Khansday/Data-collector/Codes to test each module of the system/Lidar_checksum/Lidar_checksum.ino

/*
~~~~RETRIEVE PACKETS FROM LIDAR WITH TIMOUT AND FILLS A CIRCULAR BUFFER
~~~~NEW DATA IN THE BUFFER IS READ AND PROCESSED
~~~~ ALL ANGLES ARE ROUNDED TO LOWEST 10, PACKETS REGARDING TO THAT ANGLE, THE MIN DISTNACE IS UPDATED.
*/


#include <Arduino.h>
#include "mbed.h"  // Include Mbed OS headers to apply mbed_app.json configurations

#define BUFFER_SIZE 10000 // Define the size of the buffer
byte raw_array[BUFFER_SIZE] = {0};  // Initialize the buffer

// Circular buffer indices and counters
volatile size_t read_index = 0;
volatile size_t write_index = 0;
volatile size_t buffer_count = 0;

bool new_lidar_data_flag = false;

// Modifiable time limits (in milliseconds)
unsigned long buffer_fill_time_limit = 10; // Time limit for filling the buffer
unsigned long parsing_time_limit = 2;     // Time limit for parsing the buffer

const int NUM_ANGLES = 19; // Represents angles from 0 to 180 in steps of 10 degrees
int min_distances[NUM_ANGLES];

void setup() {
  Serial.begin(500000);    // Start the serial port for logging
  Serial1.begin(230400);   // Start Serial1 to communicate with the LiDAR module

  delay(1000);
  Serial.println("Program Started");
  delay(1000);

  init_distance_array();
}

void loop() {
  // Fill the buffer with data from LiDAR for a specified time or until full
  full_raw_buffer();

  // Parse the buffer at specified intervals with a time limit
  if (new_lidar_data_flag) {
    parse_raw_buffer_min_angle();
    new_lidar_data_flag = false; // Reset the flag after parsing
  } else {
    Serial.println("No new data");
  }
}

void full_raw_buffer() {
  unsigned long start_time = millis();

  while (millis() - start_time < buffer_fill_time_limit && buffer_count < BUFFER_SIZE) {
    if (Serial1.available()) {
      int data = Serial1.read();
      if (data != -1) {
        // Check if buffer is not full
        if (buffer_count < BUFFER_SIZE) {
          raw_array[write_index++] = (byte)data;
          write_index %= BUFFER_SIZE;
          buffer_count++;
          new_lidar_data_flag = true;
        } else {
          // Buffer is full
          //Serial.println("Buffer is full, cannot write more data");
          break;
        }
      }
    }
  }

  if (millis() - start_time >= buffer_fill_time_limit) {
    //Serial.println("Buffer fill time limit reached");
  }
}

// Function to retrieve the min value from a packet, validate CRC, and update the main distance array
void parse_raw_buffer_min_angle() {
  unsigned long start_time = millis();

  const int PACKET_SIZE = 46;
  const int NUM_POINTS = 12;

  while (millis() - start_time < parsing_time_limit && buffer_count >= PACKET_SIZE) {
    // Check for packet start
    if (raw_array[read_index] == 0x54 && raw_array[(read_index + 1) % BUFFER_SIZE] == 0x2C) {
      // Ensure we have enough data for a full packet
      if (buffer_count >= PACKET_SIZE) {
        // Read packet into a temporary array
        byte packet[PACKET_SIZE];
        for (int i = 0; i < PACKET_SIZE; i++) {
          packet[i] = raw_array[(read_index + i) % BUFFER_SIZE];
        }

        // Calculate CRC8 checksum for the packet (excluding the last byte, which is the CRC)
        byte computed_crc = calculate_crc8(packet, PACKET_SIZE - 1);

        // Compare the computed CRC with the one in the packet
        if (computed_crc == packet[PACKET_SIZE - 1]) {
          // Process the packet if CRC is valid
          float start_angle = (packet[4] + (packet[5] << 8)) * 0.01;
          float end_angle = (packet[42] + (packet[43] << 8)) * 0.01;

          // Approximate start_angle to the lowest ten
          int start_angle_approx = ((int)(start_angle / 10)) * 10;

          // Check if start_angle_approx is between 0 and 180
          if (start_angle_approx >= 0 && start_angle_approx <= 180) {
            int index = start_angle_approx / 10;

            // Read data points and find the minimum distance in this packet
            int min_distance_in_packet = 8000;

            for (int j = 0; j < NUM_POINTS; j++) {
              int idx = 6 + j * 3;
              int distance = packet[idx] + (packet[idx + 1] << 8);
              // Ignore zero distances
              if (distance != 0 && distance < min_distance_in_packet) {
                min_distance_in_packet = distance;
              }
            }

            // Update the min_distances array
            min_distances[index] = min_distance_in_packet;

            Serial.print(start_angle_approx);
            Serial.print("\t\t");
            Serial.print(min_distances[index]);
            Serial.print("\t\t");
            Serial.println("1");
          }
        } else {
          // Handle CRC failure (optional logging)
          Serial.println("CRC mismatch: Packet discarded.");
        }

        // Move read_index forward by PACKET_SIZE
        read_index = (read_index + PACKET_SIZE) % BUFFER_SIZE;
        buffer_count -= PACKET_SIZE;
      } else {
        // Not enough data to read a full packet
        break;
      }
    } else {
      // Move read_index forward by 1
      read_index = (read_index + 1) % BUFFER_SIZE;
      buffer_count--;
    }
  }

  if (millis() - start_time >= parsing_time_limit) {
    //Serial.println("Parsing time limit reached");
  }
}

static const uint8_t CrcTable[256] =
{
    0x00, 0x4d, 0x9a, 0xd7, 0x79, 0x34, 0xe3, 
    0xae, 0xf2, 0xbf, 0x68, 0x25, 0x8b, 0xc6, 0x11, 0x5c, 0xa9, 0xe4, 0x33,
    0x7e, 0xd0, 0x9d, 0x4a, 0x07, 0x5b, 0x16, 0xc1, 0x8c, 0x22, 0x6f, 0xb8,
    0xf5, 0x1f, 0x52, 0x85, 0xc8, 0x66, 0x2b, 0xfc, 0xb1, 0xed, 0xa0, 0x77, 
    0x3a, 0x94, 0xd9, 0x0e, 0x43, 0xb6, 0xfb, 0x2c, 0x61, 0xcf, 0x82, 0x55,
    0x18, 0x44, 0x09, 0xde, 0x93, 0x3d, 0x70, 0xa7, 0xea, 0x3e, 0x73, 0xa4, 
    0xe9, 0x47, 0x0a, 0xdd, 0x90, 0xcc, 0x81, 0x56, 0x1b, 0xb5, 0xf8, 0x2f,
    0x62, 0x97, 0xda, 0x0d, 0x40, 0xee, 0xa3, 0x74, 0x39, 0x65, 0x28, 0xff, 
    0xb2, 0x1c, 0x51, 0x86, 0xcb, 0x21, 0x6c, 0xbb, 0xf6, 0x58, 0x15, 0xc2,
    0x8f, 0xd3, 0x9e, 0x49, 0x04, 0xaa, 0xe7, 0x30, 0x7d, 0x88, 0xc5, 0x12, 
    0x5f, 0xf1, 0xbc, 0x6b, 0x26, 0x7a, 0x37, 0xe0, 0xad, 0x03, 0x4e, 0x99,
    0xd4, 0x7c, 0x31, 0xe6, 0xab, 0x05, 0x48, 0x9f, 0xd2, 0x8e, 0xc3, 0x14, 
    0x59, 0xf7, 0xba, 0x6d, 0x20, 0xd5, 0x98, 0x4f, 0x02, 0xac, 0xe1, 0x36,
    0x7b, 0x27, 0x6a, 0xbd, 0xf0, 0x5e, 0x13, 0xc4, 0x89, 0x63, 0x20, 0xf9,
    0xb4, 0x1a, 0x57, 0x80, 0xcd, 0x91, 0xdc, 0x0b, 0x46, 0xe8, 0xa5, 0x72,
    0x3f, 0xca, 0x87, 0x50, 0x1d, 0xb3, 0xfe, 0x29, 0x64, 0x38, 0x75, 0xa2,
    0xef, 0x41, 0x0c, 0xdb, 0x96, 0x42, 0x0f, 0xd8, 0x95, 0x3b, 0x76, 0xa1,
    0xec, 0xb0, 0xfd, 0x2a, 0x67, 0xc9, 0x84, 0x53, 0x1e, 0xeb, 0xa6, 0x71, 
    0x3c, 0x92, 0xdf, 0x08, 0x45, 0x19, 0x54, 0x83, 0xce, 0x60, 0x2d, 0xfa,
    0xb7, 0x5d, 0x10, 0xc7, 0x8a, 0x24, 0x69, 0xbe, 0xf3, 0xaf, 0xe2, 0x35, 
    0x78, 0xd6, 0x9b, 0x4c, 0x01, 0xf4, 0xb9, 0x6e, 0x23, 0x8d, 0xc0, 0x17,
    0x5a, 0x06, 0x4b, 0x9c, 0xd1, 0x7f, 0x32, 0xe5, 0xa8
};


uint8_t calculate_crc8(const uint8_t *data, uint8_t len) {
    uint8_t crc = 0; // Initialize CRC to 0 as per the manual
    for (uint8_t i = 0; i < len; i++) {
        crc = CrcTable[(crc ^ data[i]) & 0xFF]; // Lookup table-based CRC
    }
    return crc;
}



void init_distance_array(){
  // Initialize min_distances with a large value
  for (int idx = 0; idx < NUM_ANGLES; idx++) {
    min_distances[idx] = 65535;
  }
}
